billbill100/Camera-Shutter-tester-Cheap-Easy-it-Works/ESP32_V4/3d_print_files/ShutterTesterFrame/Shutter Tester Sensor Enclosure102.3mf

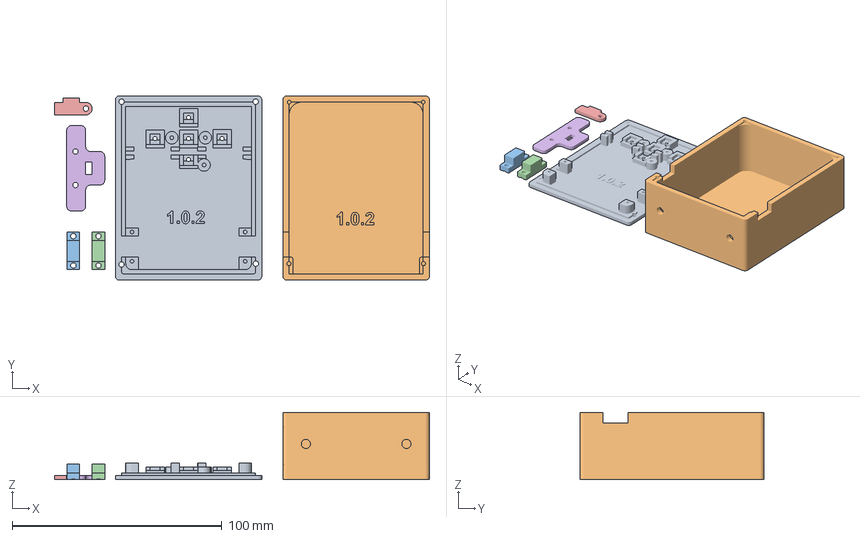
[picture p61: CAD file, 2026-03-09]
ESP32_V4/3d_print_files/ShutterTesterFrame/Shutter Tester Sensor Enclosure102.3mf
179.0 x 88.0 x 32.0 mm
clamp1
clamp2
lower sens cove
top sens cover
