billbill100/Camera-Shutter-tester-Cheap-Easy-it-Works/ESP32_V4/3d_print_files/ShutterTesterCase3dPrinted/TheShutterTesterBox v15.3mf

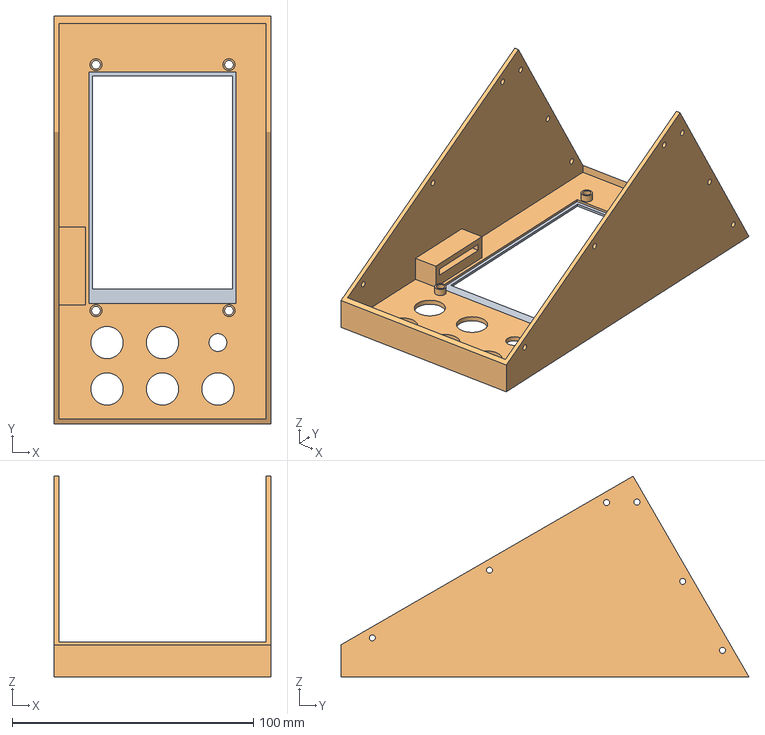
[picture p62: CAD file, 2025-11-10]
ESP32_V4/3d_print_files/ShutterTesterCase3dPrinted/TheShutterTesterBox v15.3mf
90.0 x 169.2 x 83.2 mm
