billbill100/Camera-Shutter-tester-Cheap-Easy-it-Works/ESP32_V4/3d_print_files/ShutterTesterFrame/Shutter Tester Laser Enclosure102.3mf

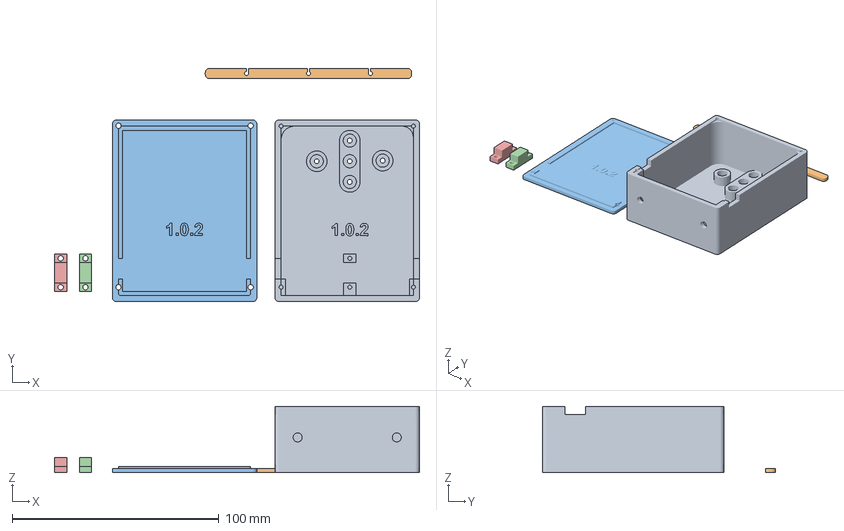
[picture p63: CAD file, 2026-03-09]
ESP32_V4/3d_print_files/ShutterTesterFrame/Shutter Tester Laser Enclosure102.3mf
176.8 x 113.0 x 32.0 mm
clamp1
clamp2
