billbill100/Camera-Shutter-tester-Cheap-Easy-it-Works/ESP32_V4/3d_print_files/ShutterTesterCase3dPrinted/TheShutterTesterRear v6.3mf

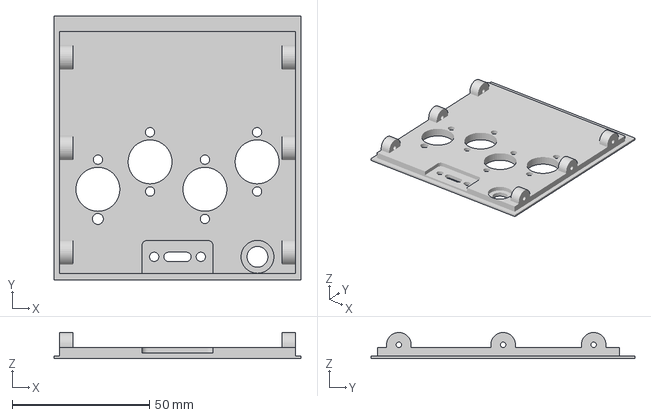
[picture p64: CAD file, 2025-11-10]
ESP32_V4/3d_print_files/ShutterTesterCase3dPrinted/TheShutterTesterRear v6.3mf
90.0 x 96.1 x 9.48 mm
