billbill100/Camera-Shutter-tester-Cheap-Easy-it-Works/ESP32_V4/3d_print_files/camera_steady/camera_steady v12.jpg

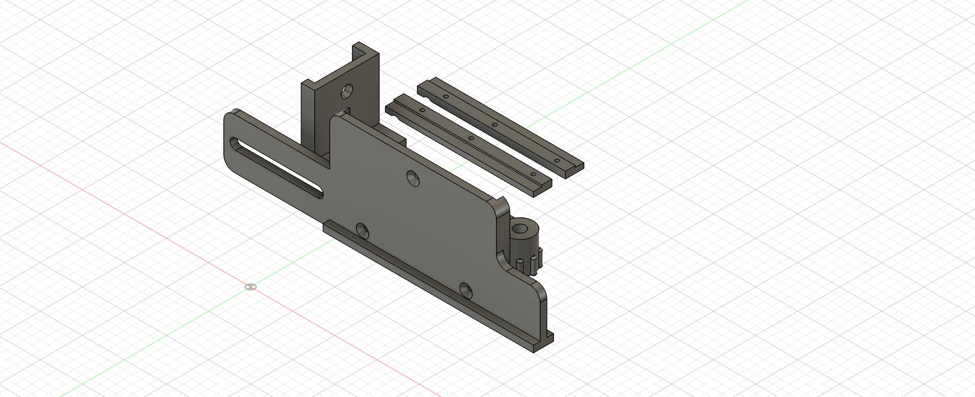
ESP32_V4/3d_print_files/camera_steady/camera_steady v12.jpg
