billbill100/Camera-Shutter-tester-Cheap-Easy-it-Works/ESP32_V4/3d_print_files/Project_box_marking_out_4_inch v3.png

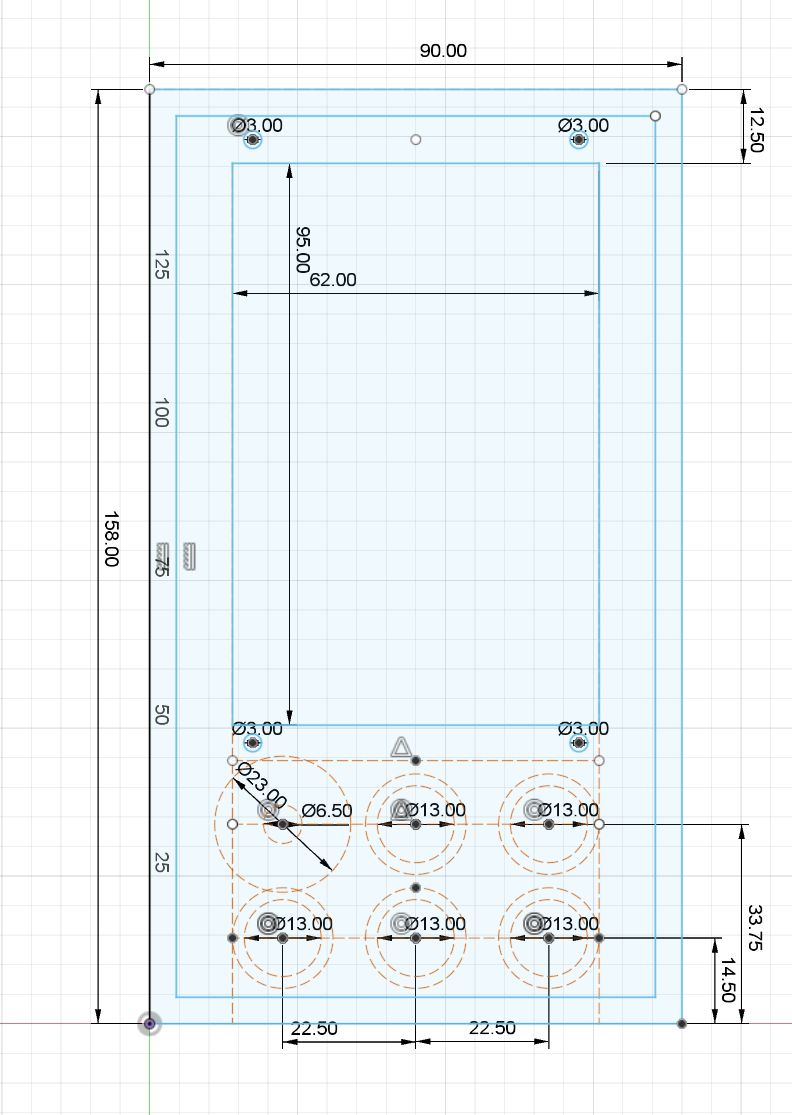
ESP32_V4/3d_print_files/Project_box_marking_out_4_inch v3.png
