billbill100/Camera-Shutter-tester-Cheap-Easy-it-Works/ESP32_V4/3d_print_files/ShutterTesterCase3dPrinted/20251104_143012.jpg

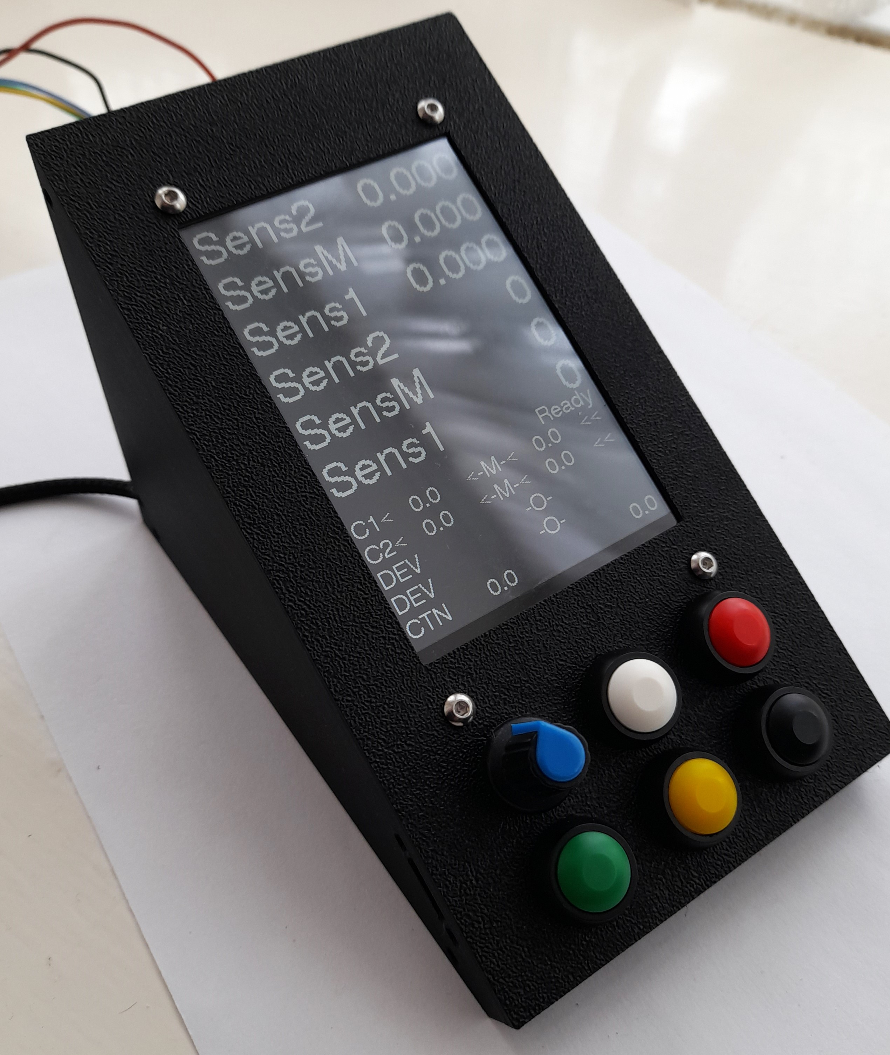
ESP32_V4/3d_print_files/ShutterTesterCase3dPrinted/20251104_143012.jpg
