billbill100/Camera-Shutter-tester-Cheap-Easy-it-Works/Arduino_V2/3d print files/Shutter_Tester_Arduino_Case v8.jpg

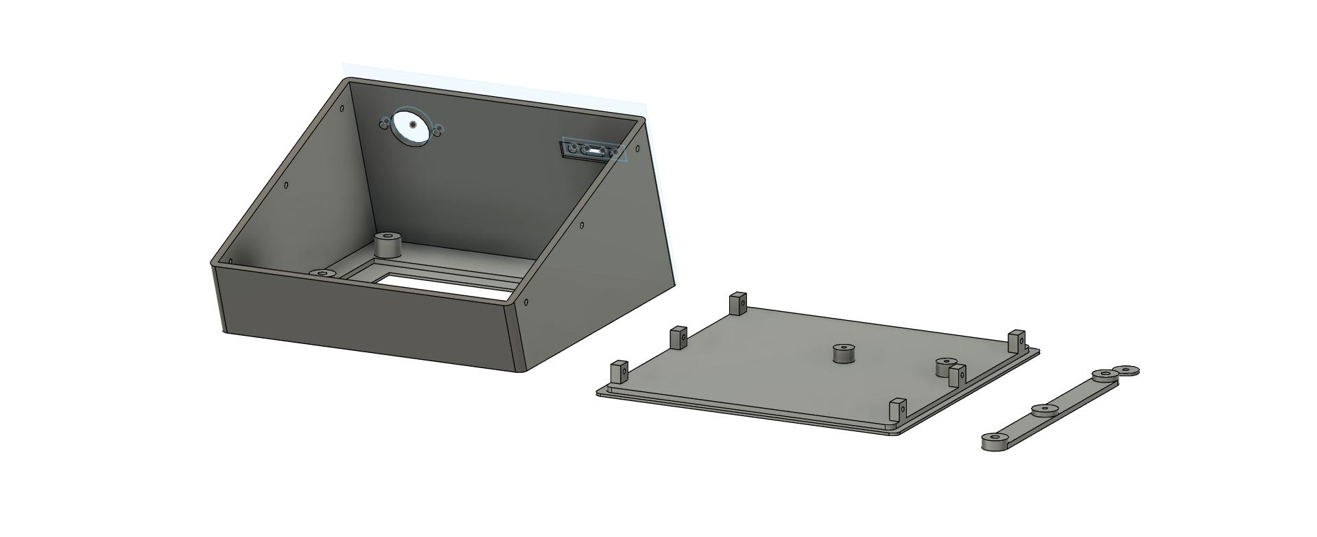
Arduino_V2/3d print files/Shutter_Tester_Arduino_Case v8.jpg
