billbill100/Camera-Shutter-tester-Cheap-Easy-it-Works/ESP32_V4/3d_print_files/Expansion board frame/TheShutterTester_tft_exp_frame v3.jpg

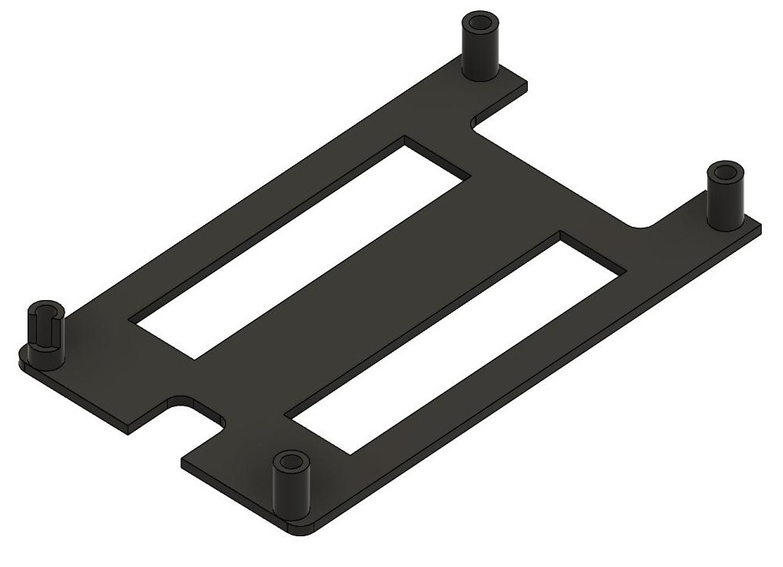
ESP32_V4/3d_print_files/Expansion board frame/TheShutterTester_tft_exp_frame v3.jpg
