billbill100/Camera-Shutter-tester-Cheap-Easy-it-Works/ESP32_V4/3d_print_files/ShutterTesterCase3dPrinted 3_5/TheShutterTester3_5_screen v10.jpg

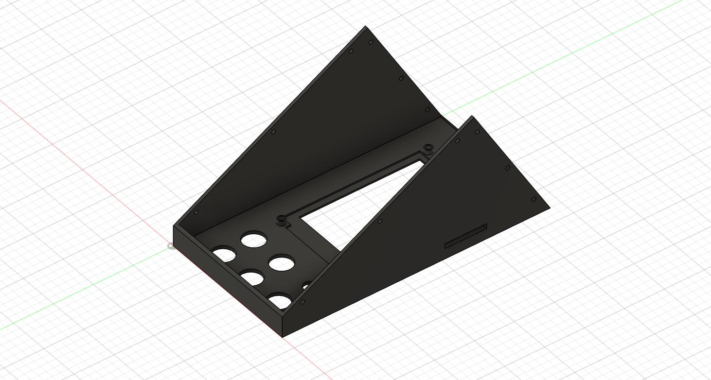
ESP32_V4/3d_print_files/ShutterTesterCase3dPrinted 3_5/TheShutterTester3_5_screen v10.jpg
