billbill100/Camera-Shutter-tester-Cheap-Easy-it-Works/ESP32_V4/3d_print_files/ShutterTesterFrame/Shutter Tester Laser Enclosure2 v5.jpg

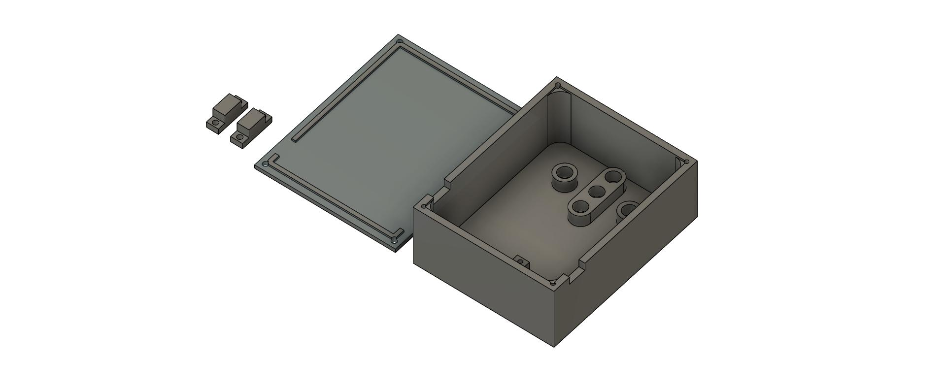
ESP32_V4/3d_print_files/ShutterTesterFrame/Shutter Tester Laser Enclosure2 v5.jpg
