billbill100/Camera-Shutter-tester-Cheap-Easy-it-Works/ESP32_V4/3d_print_files/ShutterTesterFrame/shutter_tester_base103 v2.jpg

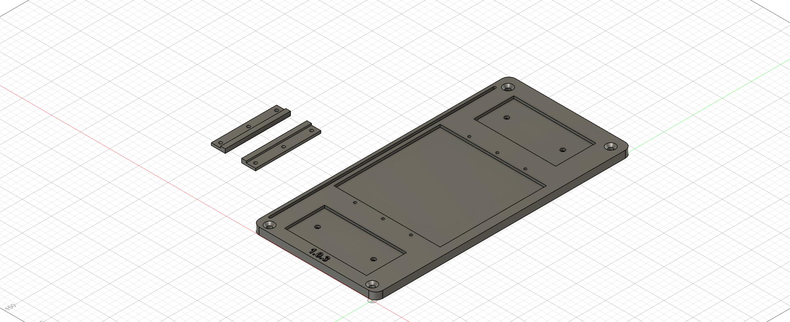
ESP32_V4/3d_print_files/ShutterTesterFrame/shutter_tester_base103 v2.jpg
