billbill100/Camera-Shutter-tester-Cheap-Easy-it-Works/Arduino_V2/Aduino_shutter_tester_V2_bb.pdf

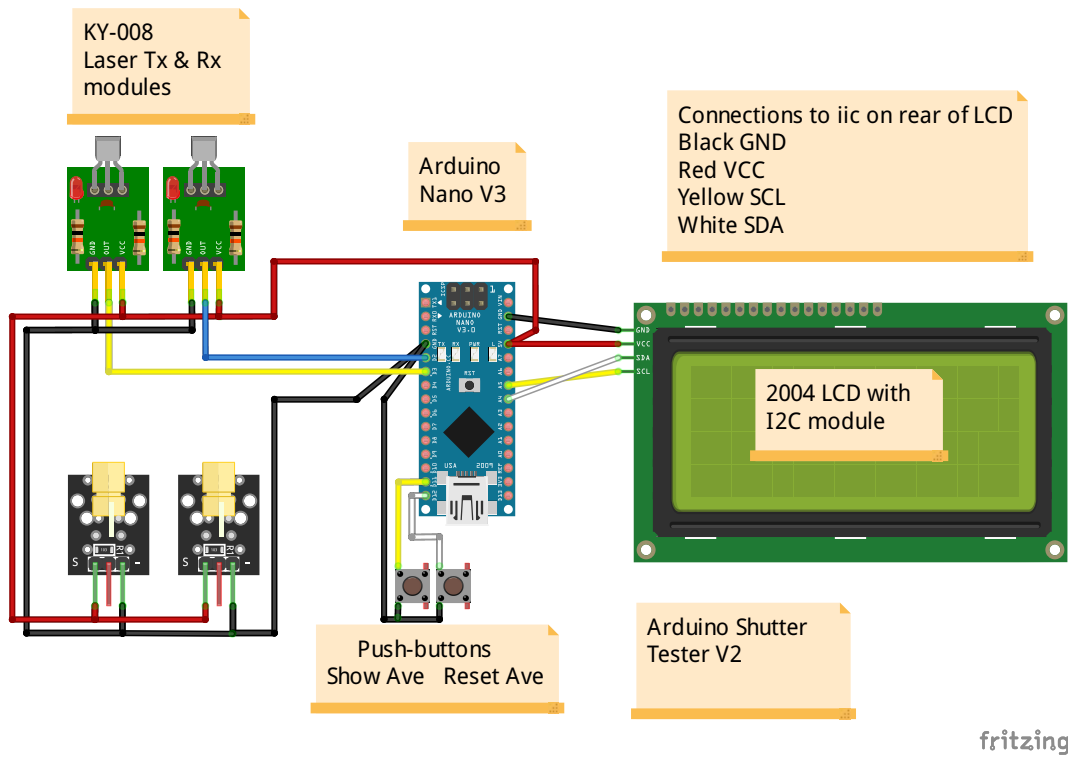
[picture p224: page 1]
2004 LCD with I2C module; Arduino Nano V3; Arduino Shutter Tester V2

Laser Tx & Rx
modules

Connections to iic on rear of LCD
Black GND
Red VCC
Yellow SCL
White SDA

Push-buttons
Show Ave Reset Ave
